altofctrl/lith/research/ui-judge/frames/deployed/anthropic_claude-haiku-4-5-20251001_rep1__1_boot_idle.png

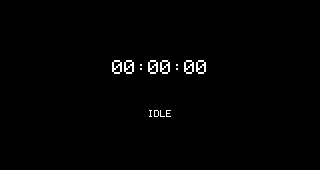
research/ui-judge/frames/deployed/anthropic_claude-haiku-4-5-20251001_rep1__1_boot_idle.png
