altofctrl/lith/research/ui-judge/frames/deployed/anthropic_claude-haiku-4-5-20251001_rep2__6_stopped.png

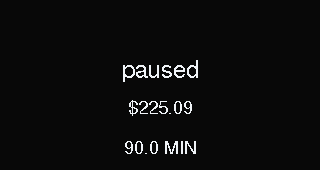
research/ui-judge/frames/deployed/anthropic_claude-haiku-4-5-20251001_rep2__6_stopped.png
