altofctrl/lith/research/ui-judge/frames/deployed/anthropic_claude-opus-5_rep1__2_started.png

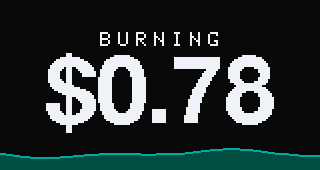
research/ui-judge/frames/deployed/anthropic_claude-opus-5_rep1__2_started.png
