altofctrl/lith/research/ui-judge/frames/deployed/anthropic_claude-opus-5_rep1__3_mid_meeting.png

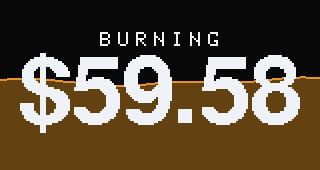
research/ui-judge/frames/deployed/anthropic_claude-opus-5_rep1__3_mid_meeting.png
