altofctrl/lith/research/ui-judge/frames/deployed/anthropic_claude-opus-5_rep1__6_stopped.png

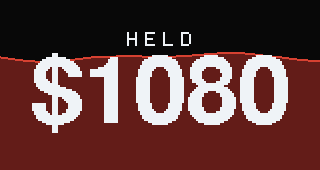
research/ui-judge/frames/deployed/anthropic_claude-opus-5_rep1__6_stopped.png
