altofctrl/lith/research/ui-judge/frames/deployed/anthropic_claude-opus-5_rep2__1_boot_idle.png

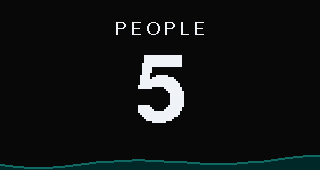
research/ui-judge/frames/deployed/anthropic_claude-opus-5_rep2__1_boot_idle.png
