altofctrl/lith/research/ui-judge/frames/deployed/anthropic_claude-opus-5_rep2__2_started.png

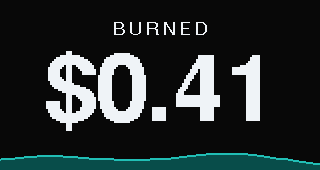
research/ui-judge/frames/deployed/anthropic_claude-opus-5_rep2__2_started.png
