altofctrl/lith/research/ui-judge/frames/deployed/anthropic_claude-opus-5_rep2__4_threshold.png

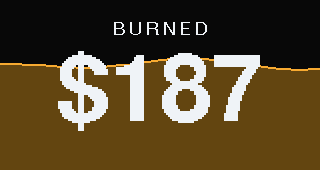
research/ui-judge/frames/deployed/anthropic_claude-opus-5_rep2__4_threshold.png
