altofctrl/lith/research/ui-judge/frames/deployed/anthropic_claude-opus-5_rep2__5_extended.png

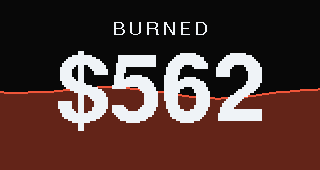
research/ui-judge/frames/deployed/anthropic_claude-opus-5_rep2__5_extended.png
