altofctrl/lith/research/ui-judge/frames/deployed/deepseek_deepseek-v4-flash_rep2__1_boot_idle.png

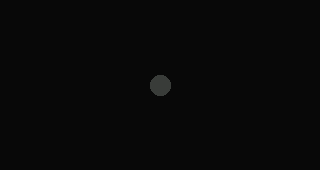
research/ui-judge/frames/deployed/deepseek_deepseek-v4-flash_rep2__1_boot_idle.png
