altofctrl/lith/research/ui-judge/frames/deployed/deepseek_deepseek-v4-flash_rep2__4_threshold.png

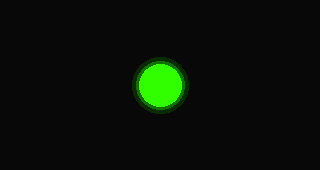
research/ui-judge/frames/deployed/deepseek_deepseek-v4-flash_rep2__4_threshold.png
