altofctrl/lith/research/ui-judge/frames/deployed/deepseek_deepseek-v4-flash_rep2__6_stopped.png

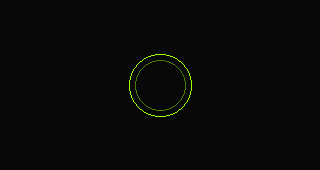
research/ui-judge/frames/deployed/deepseek_deepseek-v4-flash_rep2__6_stopped.png
