altofctrl/lith/research/ui-judge/frames/deployed/deepseek_deepseek-v4-pro_rep1__2_started.png

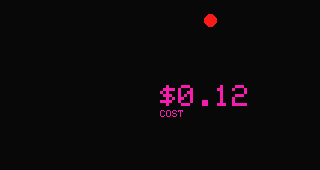
research/ui-judge/frames/deployed/deepseek_deepseek-v4-pro_rep1__2_started.png
