altofctrl/lith/research/ui-judge/frames/deployed/deepseek_deepseek-v4-pro_rep1__6_stopped.png

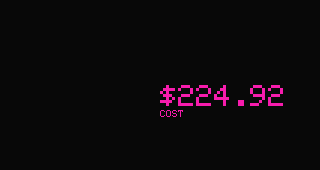
research/ui-judge/frames/deployed/deepseek_deepseek-v4-pro_rep1__6_stopped.png
