altofctrl/lith/research/ui-judge/frames/deployed/deepseek_deepseek-v4-pro_rep2__5_extended.png

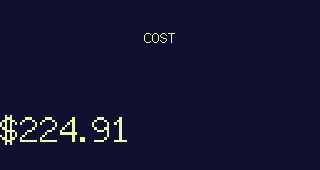
research/ui-judge/frames/deployed/deepseek_deepseek-v4-pro_rep2__5_extended.png
