altofctrl/lith/research/ui-judge/frames/deployed/groq_llama-3.3-70b-versatile_rep2__1_boot_idle.png

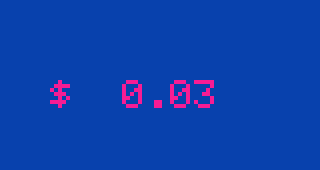
research/ui-judge/frames/deployed/groq_llama-3.3-70b-versatile_rep2__1_boot_idle.png
