altofctrl/lith/research/ui-judge/frames/deployed/groq_openai_gpt-oss-120b_rep1__1_boot_idle.png

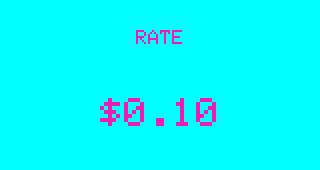
research/ui-judge/frames/deployed/groq_openai_gpt-oss-120b_rep1__1_boot_idle.png
