altofctrl/lith/research/ui-judge/frames/deployed/groq_openai_gpt-oss-120b_rep2__5_extended.png

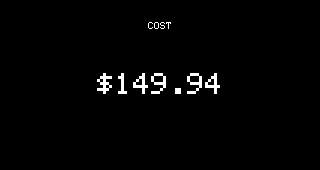
research/ui-judge/frames/deployed/groq_openai_gpt-oss-120b_rep2__5_extended.png
