altofctrl/lith/research/ui-judge/frames/deployed/openai_gpt-4.1_rep1__1_boot_idle.png

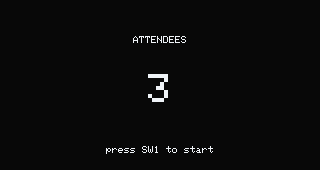
research/ui-judge/frames/deployed/openai_gpt-4.1_rep1__1_boot_idle.png
