altofctrl/lith/research/ui-judge/frames/deployed/openai_gpt-4.1_rep1__3_mid_meeting.png

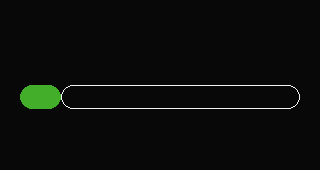
research/ui-judge/frames/deployed/openai_gpt-4.1_rep1__3_mid_meeting.png
