altofctrl/lith/research/ui-judge/frames/deployed/openai_gpt-4o-mini_rep1__2_started.png

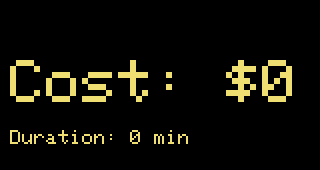
research/ui-judge/frames/deployed/openai_gpt-4o-mini_rep1__2_started.png
