altofctrl/lith/research/ui-judge/frames/deployed/openai_gpt-4o-mini_rep2__3_mid_meeting.png

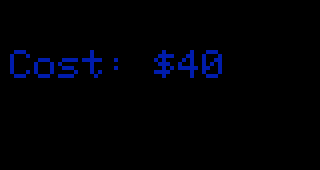
research/ui-judge/frames/deployed/openai_gpt-4o-mini_rep2__3_mid_meeting.png
