altofctrl/lith/research/ui-judge/frames/deployed/openai_gpt-5.5_rep1__1_boot_idle.png

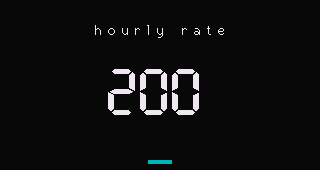
research/ui-judge/frames/deployed/openai_gpt-5.5_rep1__1_boot_idle.png
