altofctrl/lith/research/ui-judge/frames/deployed/openai_gpt-5.5_rep1__4_threshold.png

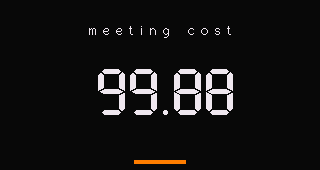
research/ui-judge/frames/deployed/openai_gpt-5.5_rep1__4_threshold.png
