altofctrl/lith/research/ui-judge/frames/deployed/openai_gpt-5.5_rep1__5_extended.png

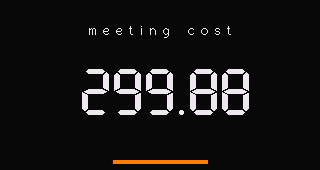
research/ui-judge/frames/deployed/openai_gpt-5.5_rep1__5_extended.png
