altofctrl/lith/research/ui-judge/frames/deployed/openai_gpt-5.5_rep2__4_threshold.png

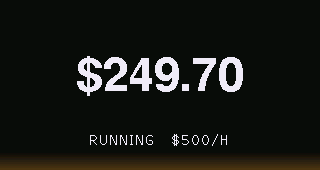
research/ui-judge/frames/deployed/openai_gpt-5.5_rep2__4_threshold.png
