altofctrl/lith/research/ui-judge/frames/deployed_x4/anthropic_claude-haiku-4-5-20251001_rep1__6_stopped.png

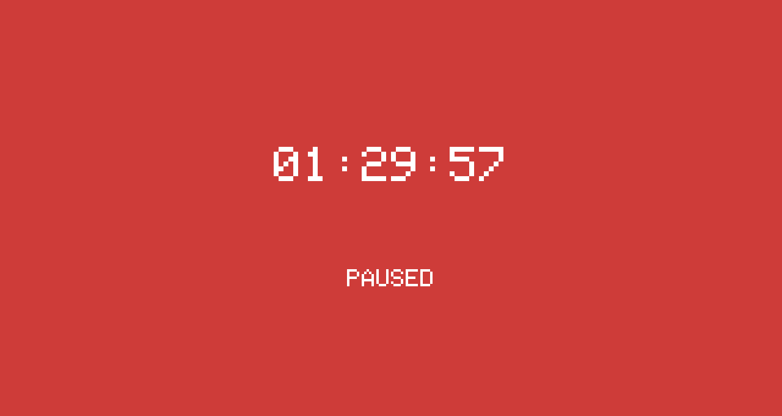
research/ui-judge/frames/deployed_x4/anthropic_claude-haiku-4-5-20251001_rep1__6_stopped.png
