altofctrl/lith/research/ui-judge/frames/deployed_x4/openai_gpt-5.5_rep1__2_started.png

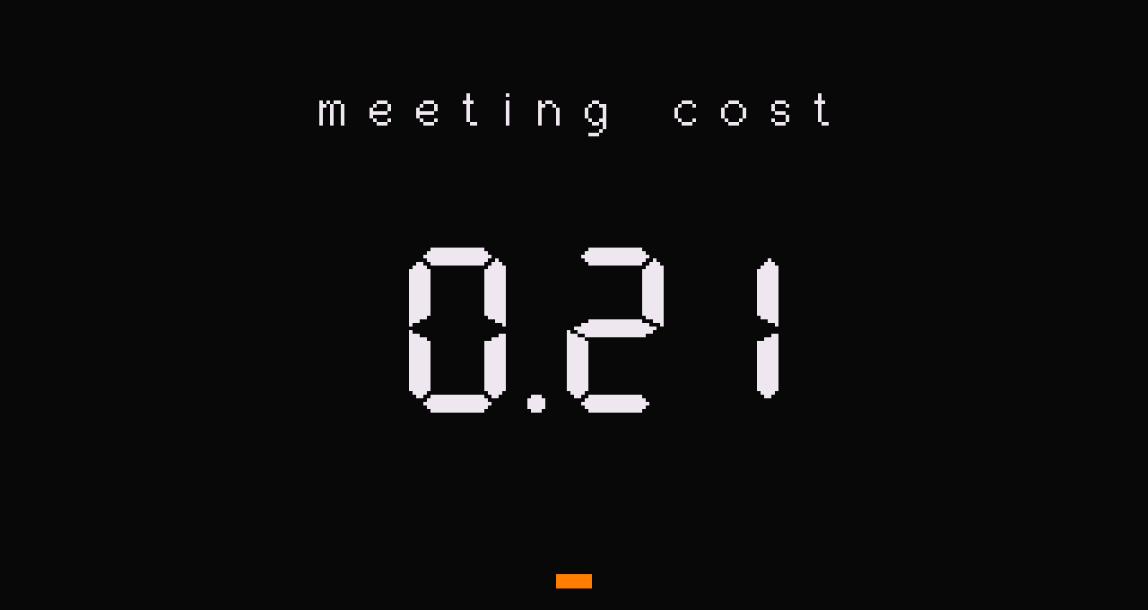
research/ui-judge/frames/deployed_x4/openai_gpt-5.5_rep1__2_started.png
