altofctrl/lith/research/ui-judge/frames/firstpass/deepseek_deepseek-v4-pro_rep2__4_threshold.png

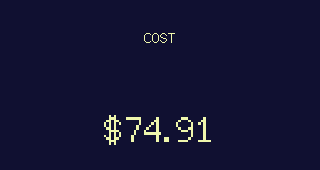
research/ui-judge/frames/firstpass/deepseek_deepseek-v4-pro_rep2__4_threshold.png
