altofctrl/lith/research/ui-judge/frames/firstpass/deepseek_deepseek-v4-pro_rep2__6_stopped.png

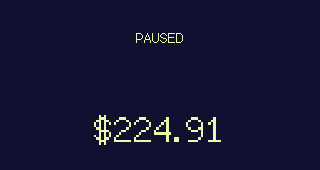
research/ui-judge/frames/firstpass/deepseek_deepseek-v4-pro_rep2__6_stopped.png
