altofctrl/lith/website/assets/frames-pcb/pcb_000.webp

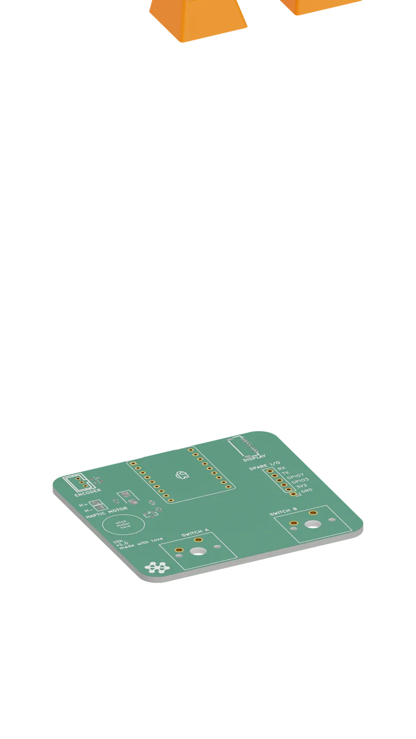
website/assets/frames-pcb/pcb_000.webp
