altofctrl/lith/website/assets/frames-pcb/pcb_016.webp

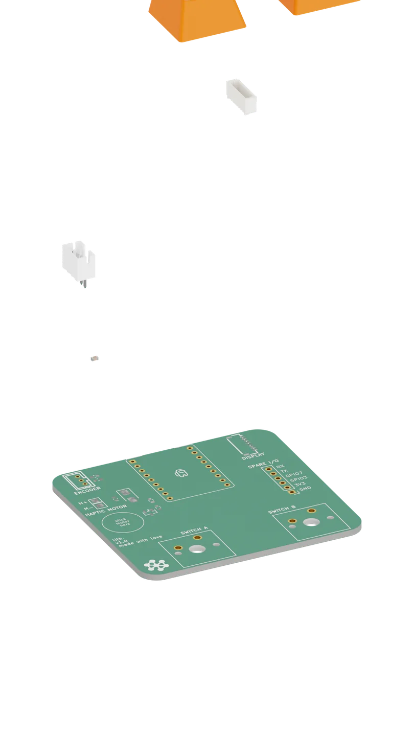
website/assets/frames-pcb/pcb_016.webp
