altofctrl/lith/website/assets/frames-pcb/pcb_019.webp

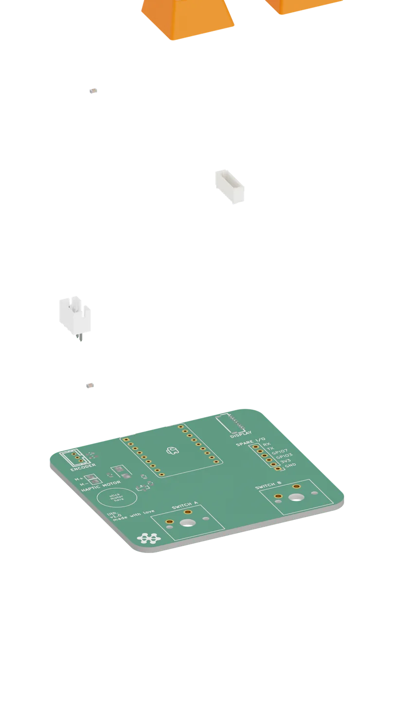
website/assets/frames-pcb/pcb_019.webp
