altofctrl/lith/website/assets/frames-pcb/pcb_022.webp

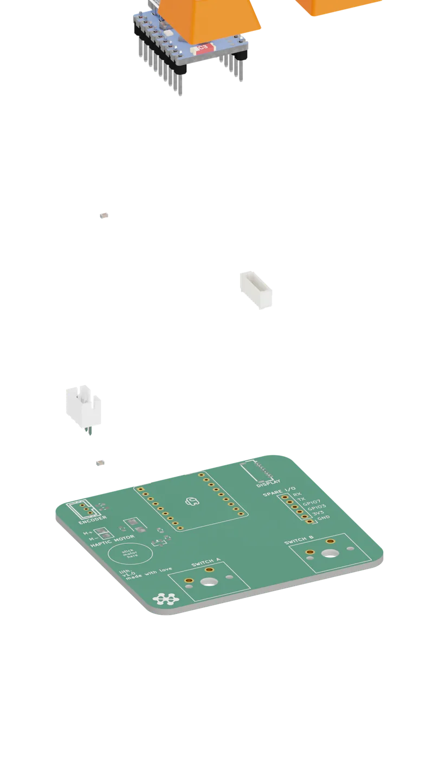
website/assets/frames-pcb/pcb_022.webp
