altofctrl/lith/website/assets/frames-pcb/pcb_023.webp

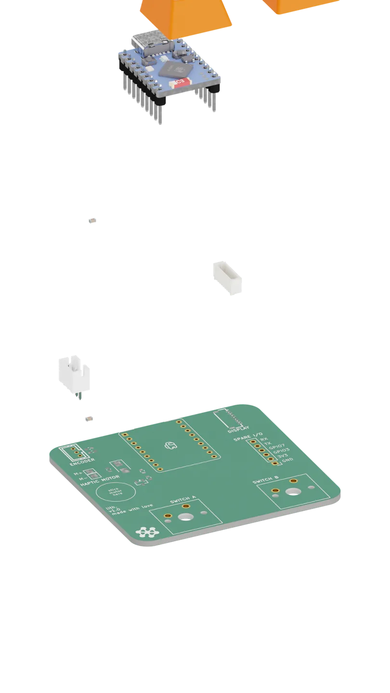
website/assets/frames-pcb/pcb_023.webp
