altofctrl/lith/website/assets/frames-pcb/pcb_025.webp

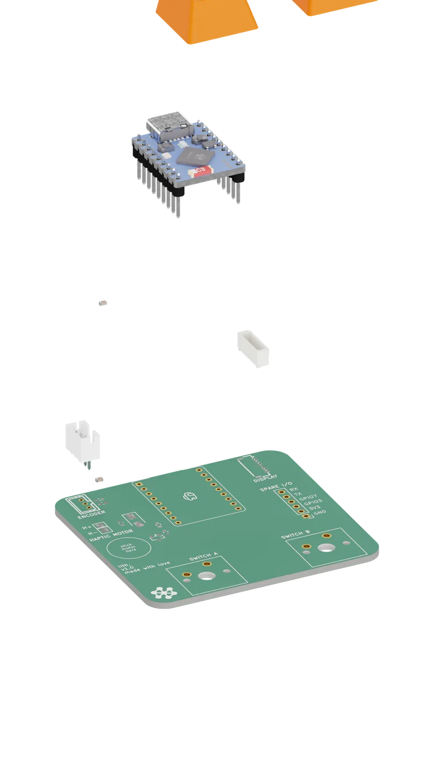
website/assets/frames-pcb/pcb_025.webp
