altofctrl/lith/website/assets/frames-pcb/pcb_028.webp

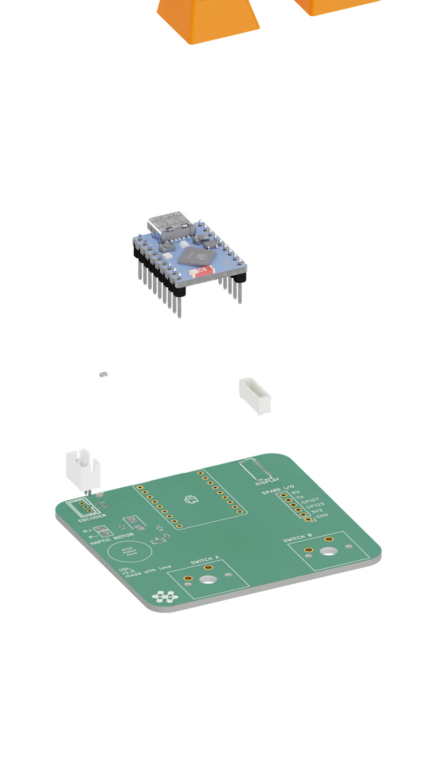
website/assets/frames-pcb/pcb_028.webp
