altofctrl/lith/website/assets/frames-pcb/pcb_038.webp

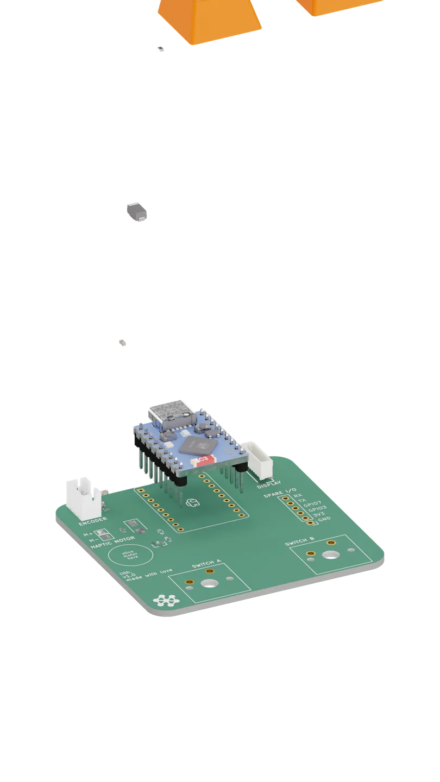
website/assets/frames-pcb/pcb_038.webp
