altofctrl/lith/website/assets/frames-pcb/pcb_050.webp

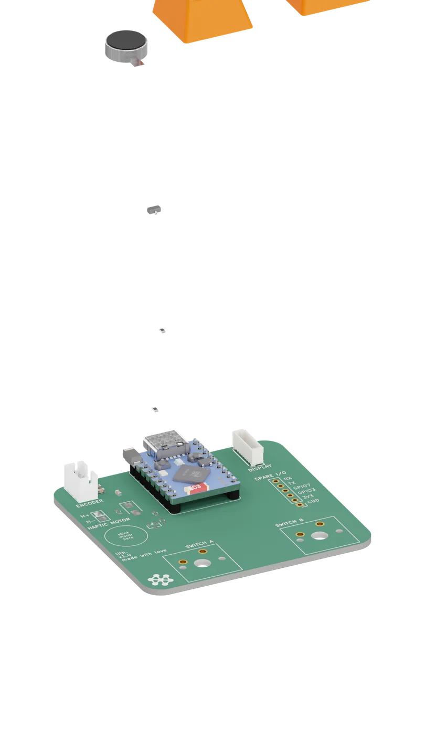
website/assets/frames-pcb/pcb_050.webp
