altofctrl/lith/website/assets/frames-pcb/pcb_051.webp

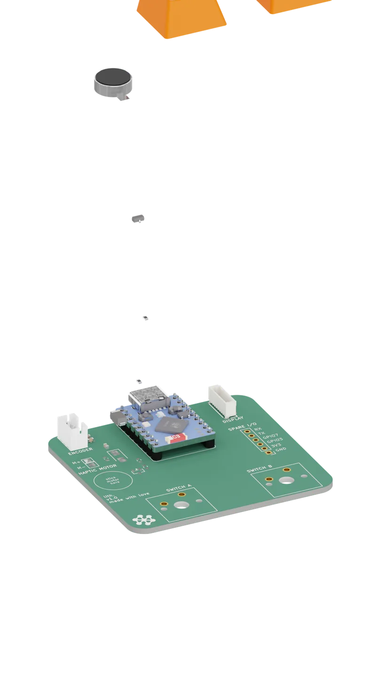
website/assets/frames-pcb/pcb_051.webp
