altofctrl/lith/website/assets/frames-pcb/pcb_053.webp

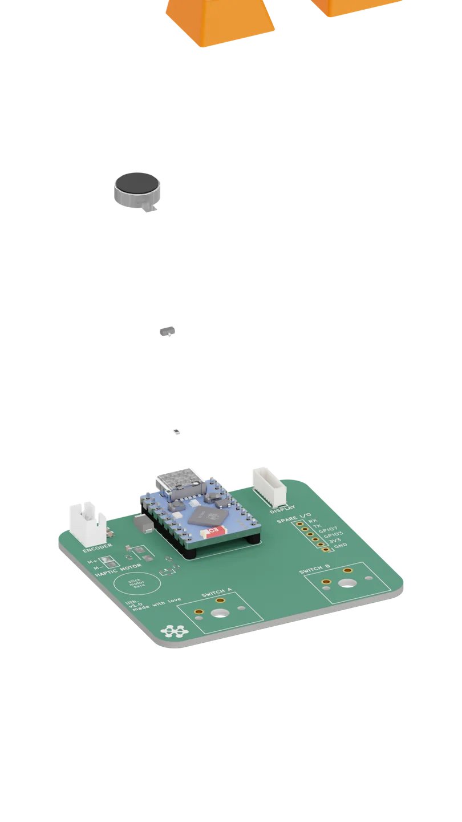
website/assets/frames-pcb/pcb_053.webp
