altofctrl/lith/website/assets/frames-pcb/pcb_055.webp

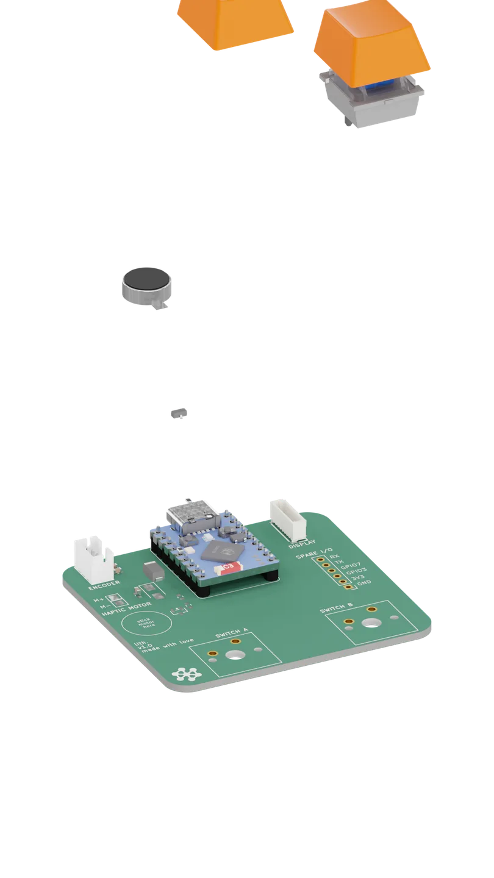
website/assets/frames-pcb/pcb_055.webp
