altofctrl/lith/website/assets/frames-pcb/pcb_057.webp

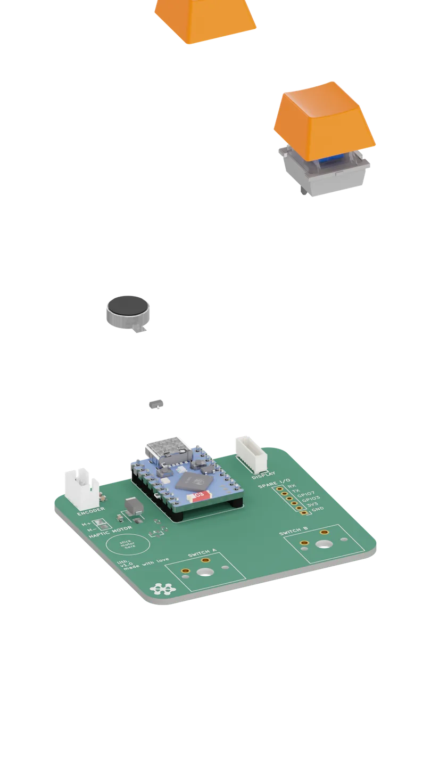
website/assets/frames-pcb/pcb_057.webp
