altofctrl/lith/website/assets/frames-pcb/pcb_058.webp

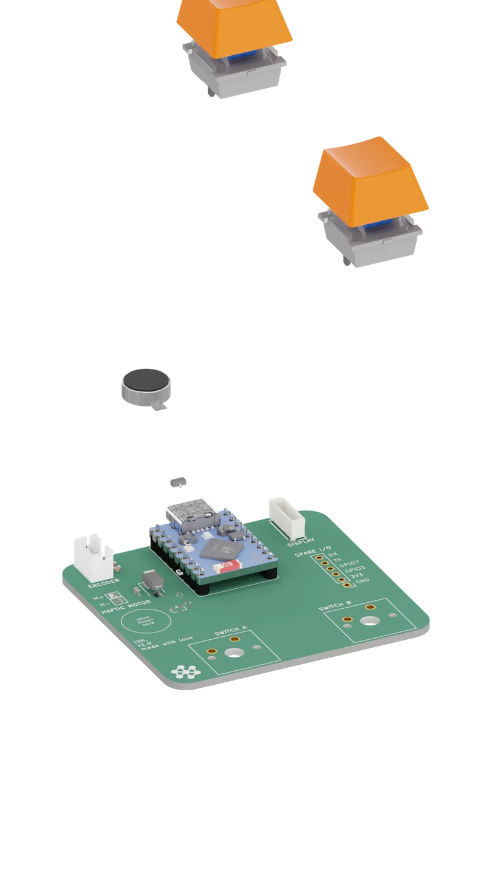
website/assets/frames-pcb/pcb_058.webp
