altofctrl/lith/website/assets/frames-pcb/pcb_060.webp

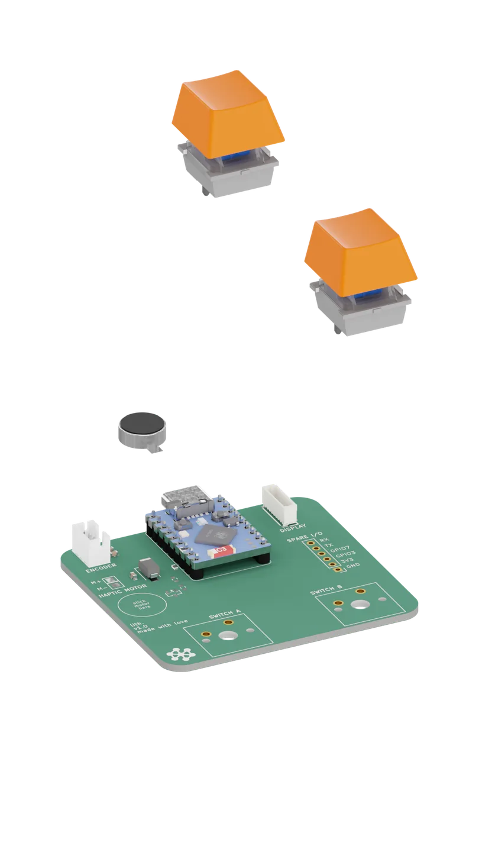
website/assets/frames-pcb/pcb_060.webp
