altofctrl/lith/website/assets/frames-pcb/pcb_061.webp

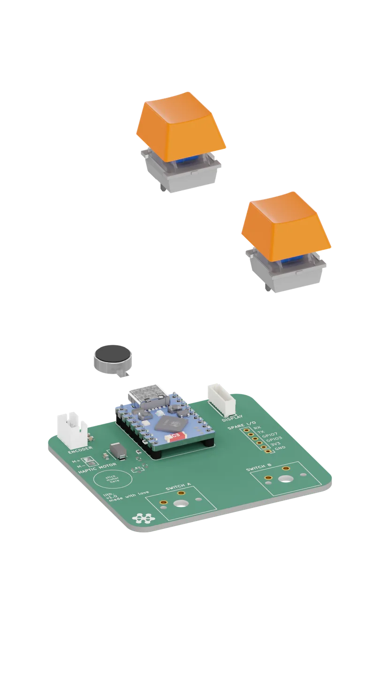
website/assets/frames-pcb/pcb_061.webp
