altofctrl/lith/website/assets/frames-pcb/pcb_064.webp

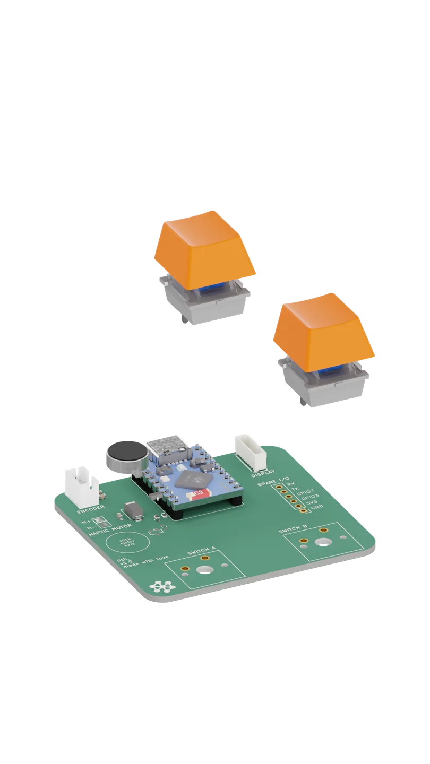
website/assets/frames-pcb/pcb_064.webp
