altofctrl/lith/website/assets/frames-pcb/pcb_067.webp

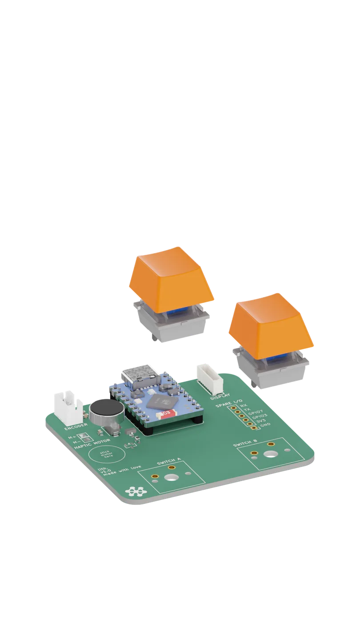
website/assets/frames-pcb/pcb_067.webp
