altofctrl/lith/website/assets/frames-pcb/pcb_072.webp

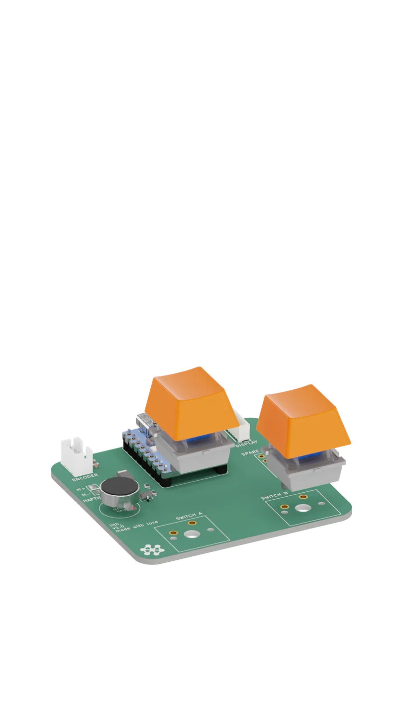
website/assets/frames-pcb/pcb_072.webp
