altofctrl/lith/website/assets/lith_v1_on.webp

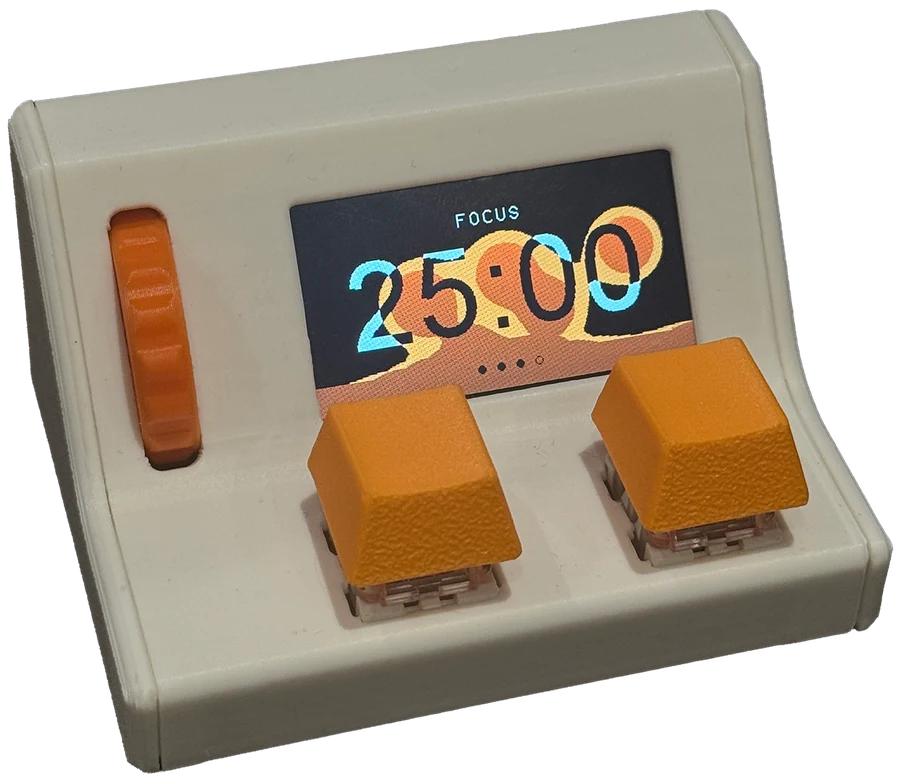
website/assets/lith_v1_on.webp
