altofctrl/lith/website/assets/lith_v1_render.webp

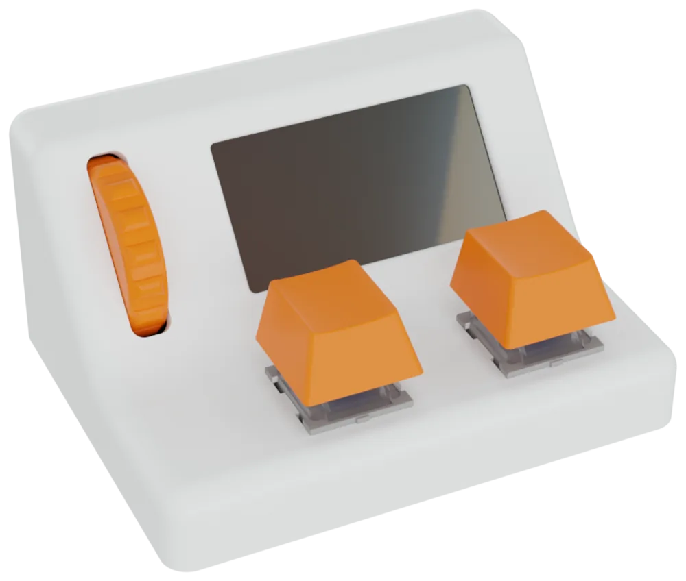
website/assets/lith_v1_render.webp
