altofctrl/lith/research/ui-judge/results/gate2_render_firstpass.csv

build_id | sim_build_ok | ran_ok | timed_out | init_called | rotation_set | rotation | panel_w | panel_h | loops | motor_writes | frames_present | distinct_frames | blank_frames | ink_1_boot_idle | ink_2_started | ink_3_mid_meeting | ink_4_threshold | ink_5_extended | ink_6_stopped | note
anthropic_claude-haiku-4-5-20251001_rep1 | False | False |  |  |  |  |  |  |  |  | 0 | 0 | 0 |  |  |  |  |  |  | A:/bridge/oldowan-ui-judge-microstudy/results/prepared_firstpass/anthropic_claude-haiku-4-5-20251001_rep1.cpp:181:26: error: 'Font7_GLCD_M' is not a member of 'fonts'
anthropic_claude-haiku-4-5-20251001_rep2 | False | False |  |  |  |  |  |  |  |  | 0 | 0 | 0 |  |  |  |  |  |  | A:/bridge/oldowan-ui-judge-microstudy/results/prepared_firstpass/anthropic_claude-haiku-4-5-20251001_rep2.cpp:54:23: error: no matching function for call to 'lgfx::v1::LGFX_Sprite::LGFX_Sprite(LGFX&)'
anthropic_claude-opus-5_rep1 | True | True | 0 | 1 | 1 | 1 | 320 | 170 | 5708 | 0 | 6 | 6 | 0 | 0.1303 | 0.2495 | 0.5999 | 0.5825 | 0.5046 | 0.51
anthropic_claude-opus-5_rep2 | True | True | 0 | 1 | 1 | 1 | 320 | 170 | 5708 | 0 | 6 | 6 | 0 | 0.0872 | 0.2124 | 0.3603 | 0.4832 | 0.5467 | 0.5463
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
