altofctrl/lith/research/ui-judge/results/judge_absolute.csv

frame | build_id | state | judge | n_reps_parsed | ease_of_use | clarity | visual_hierarchy | memorable | trust | intuitive | aesthetic_pleasure | interest | comfort
anthropic_claude-haiku-4-5-20251001_rep1__1_boot_idle.png | anthropic_claude-haiku-4-5-20251001_rep1 | 1_boot_idle | claude-sonnet-5 | 3 | 6 | 7 | 6 | 5 | 5 | 6 | 5 | 3 | 5
anthropic_claude-haiku-4-5-20251001_rep1__1_boot_idle.png | anthropic_claude-haiku-4-5-20251001_rep1 | 1_boot_idle | gpt-4.1 | 3 | 6 | 7 | 6 | 5 | 6 | 6 | 5 | 3 | 6
anthropic_claude-haiku-4-5-20251001_rep1__1_boot_idle.png | anthropic_claude-haiku-4-5-20251001_rep1 | 1_boot_idle | qwen3.6-27b | 3 | 6 | 7 | 6 | 3 | 5 | 7 | 3 | 2 | 5
anthropic_claude-haiku-4-5-20251001_rep1__2_started.png | anthropic_claude-haiku-4-5-20251001_rep1 | 2_started | claude-sonnet-5 | 3 | 6 | 7 | 6 | 5 | 5 | 6 | 4 | 3 | 6
anthropic_claude-haiku-4-5-20251001_rep1__2_started.png | anthropic_claude-haiku-4-5-20251001_rep1 | 2_started | gpt-4.1 | 3 | 7 | 7 | 6 | 5 | 6 | 6 | 4 | 3 | 6
anthropic_claude-haiku-4-5-20251001_rep1__2_started.png | anthropic_claude-haiku-4-5-20251001_rep1 | 2_started | qwen3.6-27b | 2 | 6.5 | 7.0 | 5.5 | 4.0 | 5.5 | 7.0 | 4.5 | 2.5 | 6.0
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
