altofctrl/lith/research/ui-judge/results/judge_pairwise.csv

provider | build_a | build_b | state | judge | criterion | winner | consistent
anthropic | anthropic_claude-haiku-4-5-20251001_rep1 | anthropic_claude-haiku-4-5-20251001_rep2 | 1_boot_idle | claude-sonnet-5 | aesthetic_pleasure | anthropic_claude-haiku-4-5-20251001_rep1 | True
anthropic | anthropic_claude-haiku-4-5-20251001_rep1 | anthropic_claude-opus-5_rep1 | 1_boot_idle | claude-sonnet-5 | aesthetic_pleasure | anthropic_claude-opus-5_rep1 | True
anthropic | anthropic_claude-haiku-4-5-20251001_rep1 | anthropic_claude-opus-5_rep2 | 1_boot_idle | claude-sonnet-5 | aesthetic_pleasure | anthropic_claude-opus-5_rep2 | True
anthropic | anthropic_claude-haiku-4-5-20251001_rep1 | anthropic_claude-haiku-4-5-20251001_rep2 | 1_boot_idle | claude-sonnet-5 | clarity | tie | False
anthropic | anthropic_claude-haiku-4-5-20251001_rep1 | anthropic_claude-opus-5_rep1 | 1_boot_idle | claude-sonnet-5 | clarity | tie | False
anthropic | anthropic_claude-haiku-4-5-20251001_rep1 | anthropic_claude-opus-5_rep2 | 1_boot_idle | claude-sonnet-5 | clarity | anthropic_claude-haiku-4-5-20251001_rep1 | True
anthropic | anthropic_claude-haiku-4-5-20251001_rep1 | anthropic_claude-haiku-4-5-20251001_rep2 | 1_boot_idle | claude-sonnet-5 | comfort | tie | False
anthropic | anthropic_claude-haiku-4-5-20251001_rep1 | anthropic_claude-opus-5_rep1 | 1_boot_idle | claude-sonnet-5 | comfort | tie | False
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
anthropic | anthropic_claude-opus-5_rep1 | anthropic_claude-opus-5_rep2 | 2_started | gpt-4.1 | aesthetic_pleasure | tie | False
anthropic | anthropic_claude-opus-5_rep1 | anthropic_claude-opus-5_rep2 | 2_started | gpt-4.1 | clarity | tie | False
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
