altofctrl/lith/research/ui-judge/results/contact_sheet.png

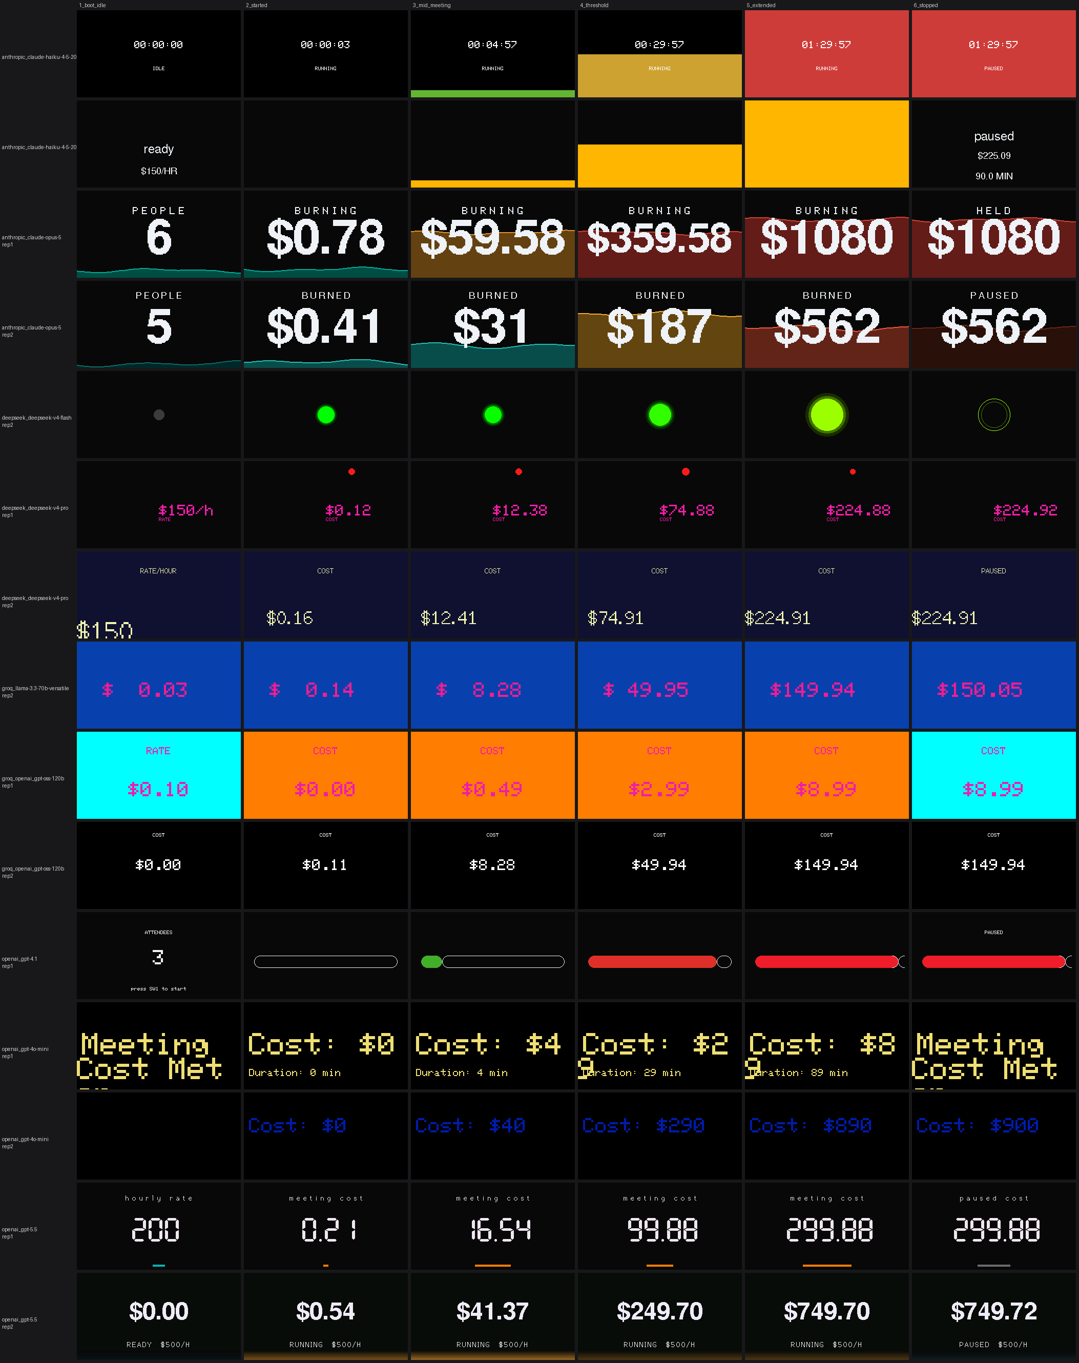
research/ui-judge/results/contact_sheet.png
